gowenrw/BSidesDFW_2019_Badge/eda/BSidesDFW_2019/3d_models/README.md

# 3d_models

This directory is for .STEP and .WRL model files for all footprints
