gowenrw/BSidesDFW_2019_Badge/eda/BSidesDFW_2019/gerber/README.md

# gerber

This directory is for the gerber formatted files to be sent to manufacturing
