gowenrw/BSidesDFW_2019_Badge/eda/BSidesDFW_2019/lib_fp/README.md

# lib_fp

This directory is for footprints

This local library contains footprints for the components used as well as the silkscreen art.
