gowenrw/BSidesDFW_2019_Badge/eda/BSidesDFW_2019/lib_sh/README.md

# lib_sch

This directory is for schematic symbols
