gowenrw/BSidesDFW_2019_Badge/eda/BSidesDFW_2019/pdf/BSidesDFW_2019-as_built-red.gif

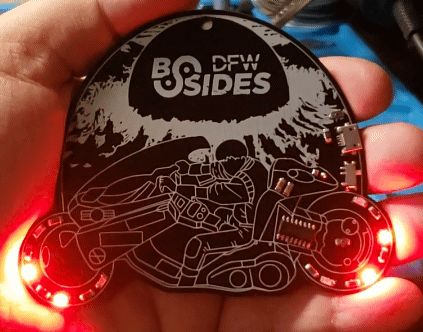
eda/BSidesDFW_2019/pdf/BSidesDFW_2019-as_built-red.gif
