gowenrw/BSidesDFW_2019_Badge/eda/BSidesDFW_2019/pdf/BSidesDFW_2019-as_built.jpg

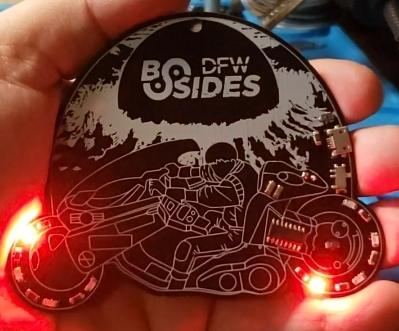
eda/BSidesDFW_2019/pdf/BSidesDFW_2019-as_built.jpg
