gowenrw/BSidesDFW_2019_Badge/eda/BSidesDFW_2019/pdf/BSidesDFW_2019_Back_Bare.png

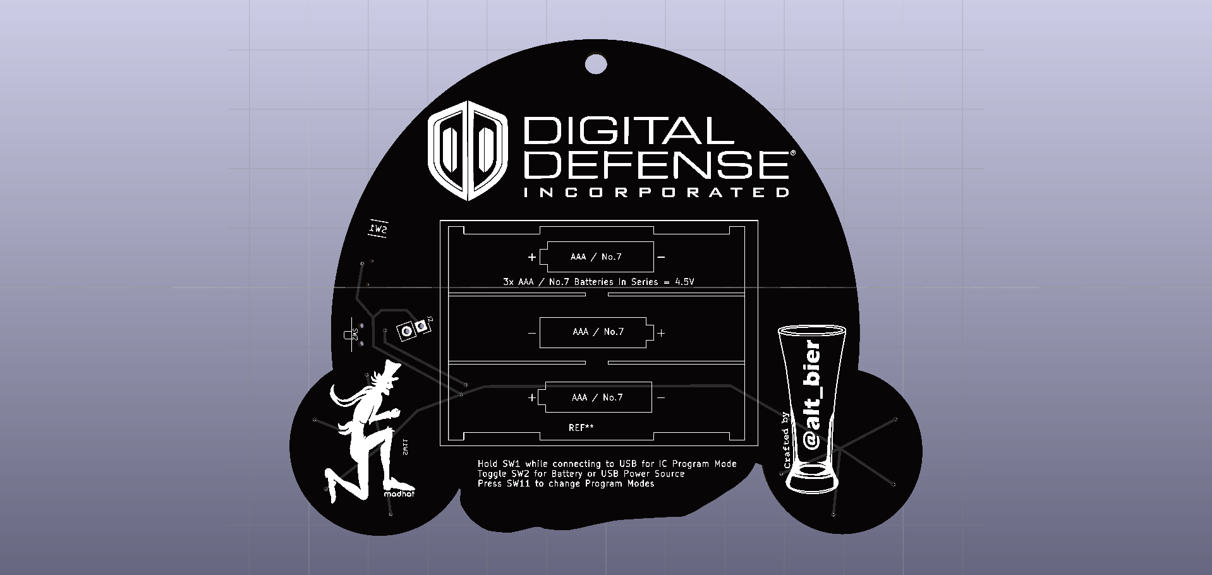
eda/BSidesDFW_2019/pdf/BSidesDFW_2019_Back_Bare.png
