gowenrw/BSidesDFW_2019_Badge/eda/BSidesDFW_2019/pdf/BSidesDFW_2019_Front_Bare.png

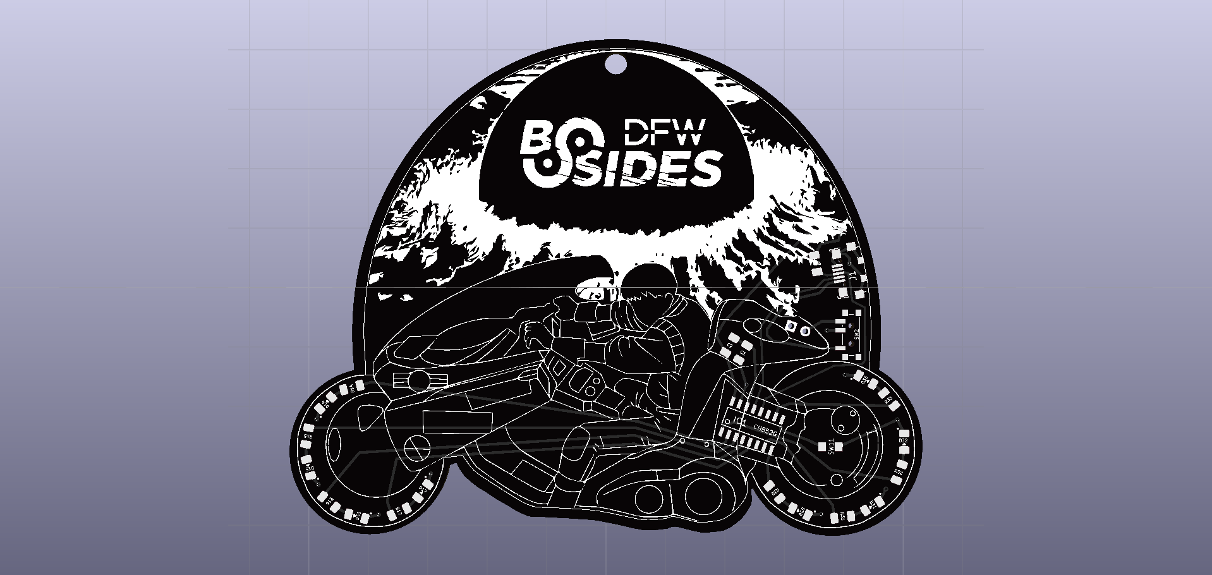
eda/BSidesDFW_2019/pdf/BSidesDFW_2019_Front_Bare.png
