gowenrw/BSidesDFW_2019_Badge/eda/BSidesDFW_2019/pdf/BSidesDFW_2019_pcb-layout_all-layers.png

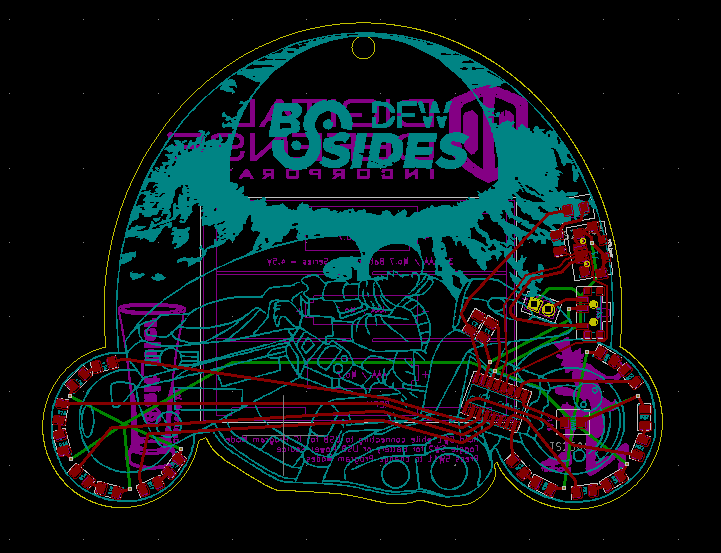
eda/BSidesDFW_2019/pdf/BSidesDFW_2019_pcb-layout_all-layers.png
