gowenrw/BSidesDFW_2019_Badge/eda/CH552G_dev/pdf/CH552G_dev.jpg

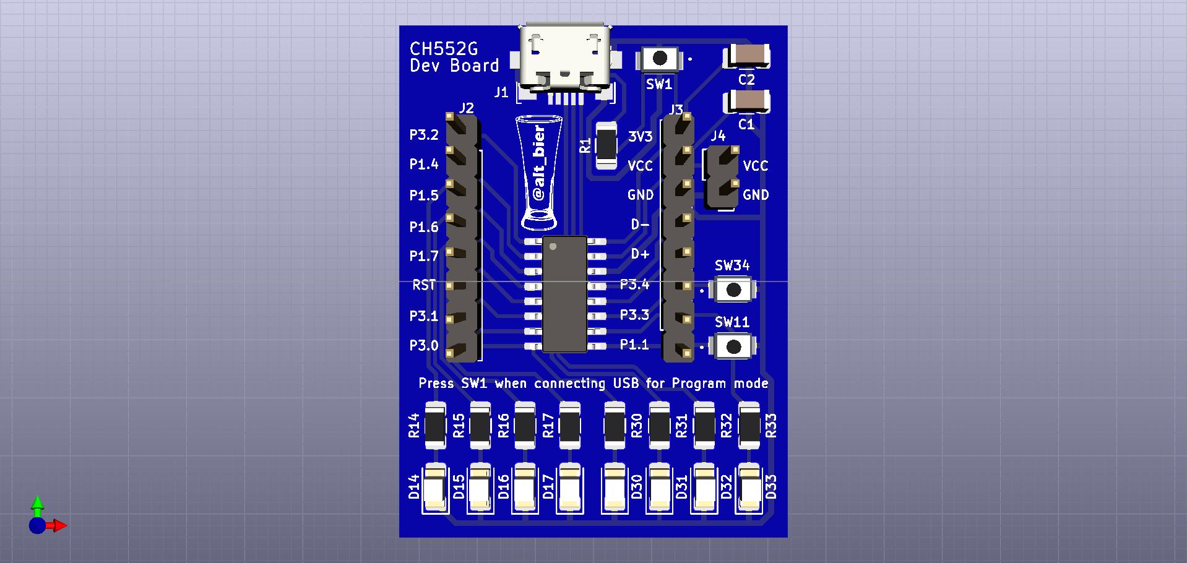
eda/CH552G_dev/pdf/CH552G_dev.jpg
