gowenrw/BSidesDFW_2019_Badge/eda/CH552G_dev/pdf/CH552G_dev_board-as_built-green.gif

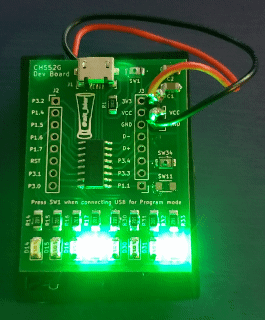
eda/CH552G_dev/pdf/CH552G_dev_board-as_built-green.gif
