gowenrw/BSidesDFW_2019_Badge/eda/HHV_2019_SC/pdf/HHV_2019_SC-as_built.jpg

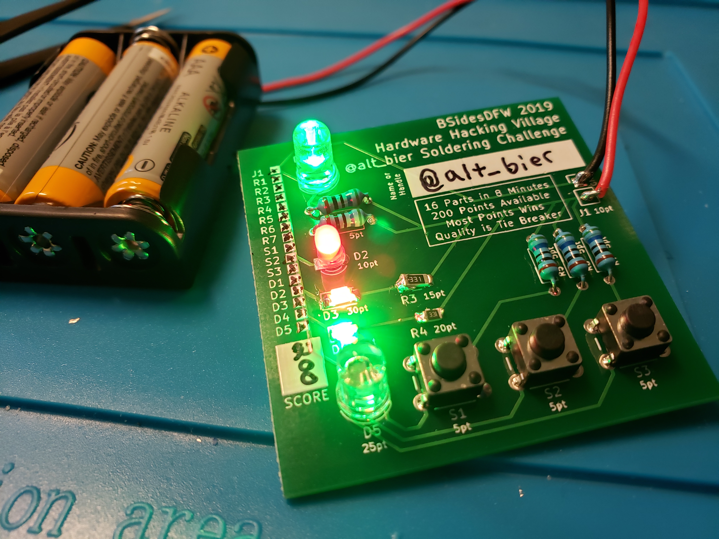
eda/HHV_2019_SC/pdf/HHV_2019_SC-as_built.jpg
