gowenrw/BSidesDFW_2019_Badge/graphics/Asset 1.png

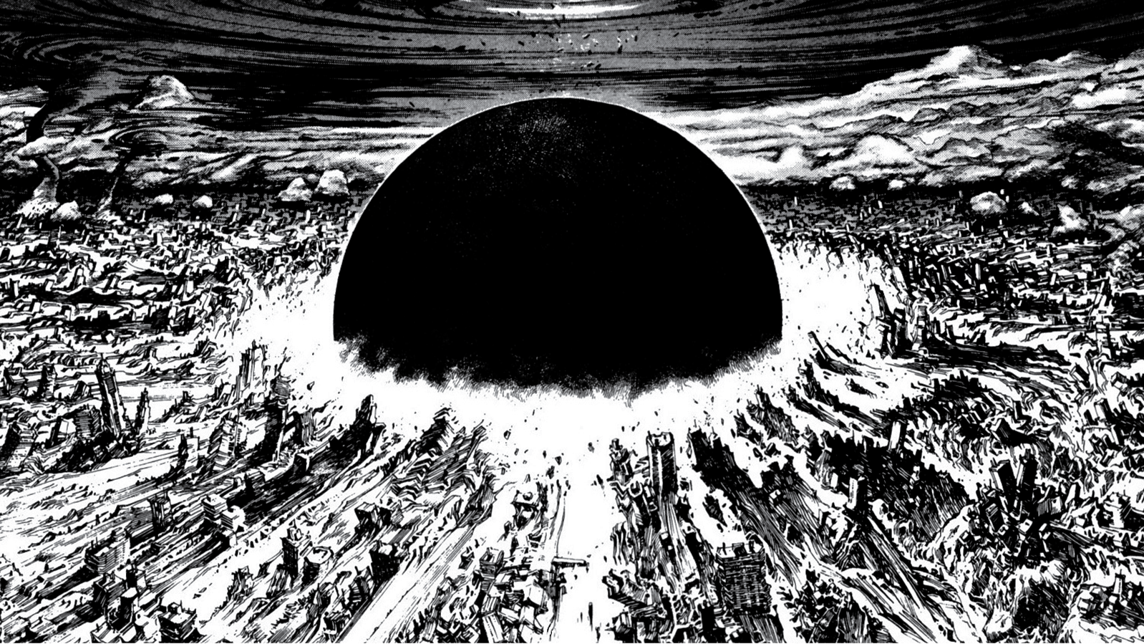
graphics/Asset 1.png
