gowenrw/BSidesDFW_2019_Badge/graphics/Asset 2.png

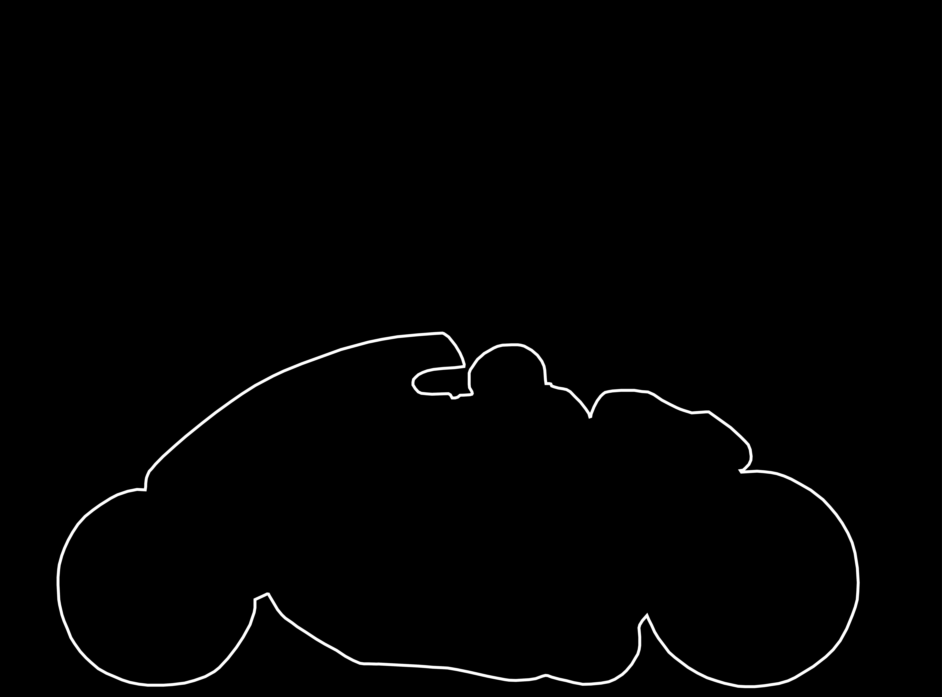
graphics/Asset 2.png
