gowenrw/BSidesDFW_2019_Badge/graphics/Asset 3.png

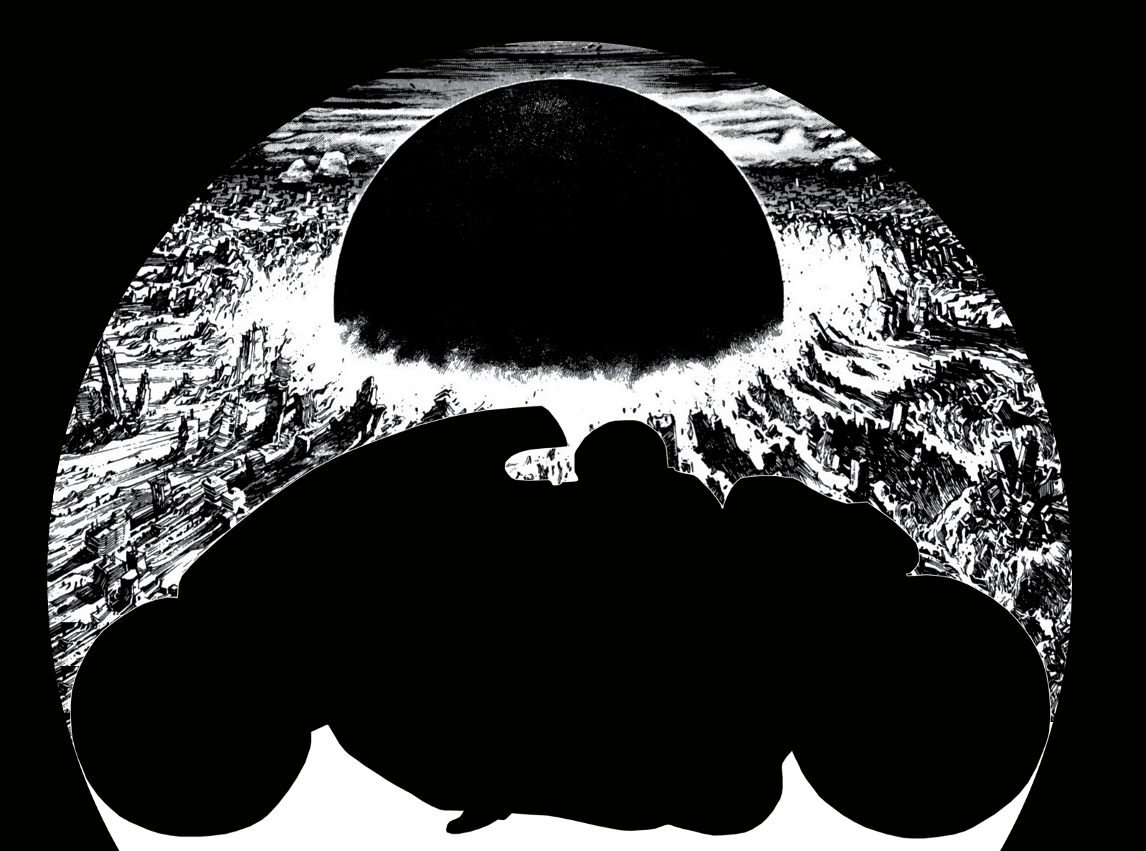
graphics/Asset 3.png
