gowenrw/BSidesDFW_2019_Badge/graphics/BSidesDFW2019_Lanyand-01.jpg

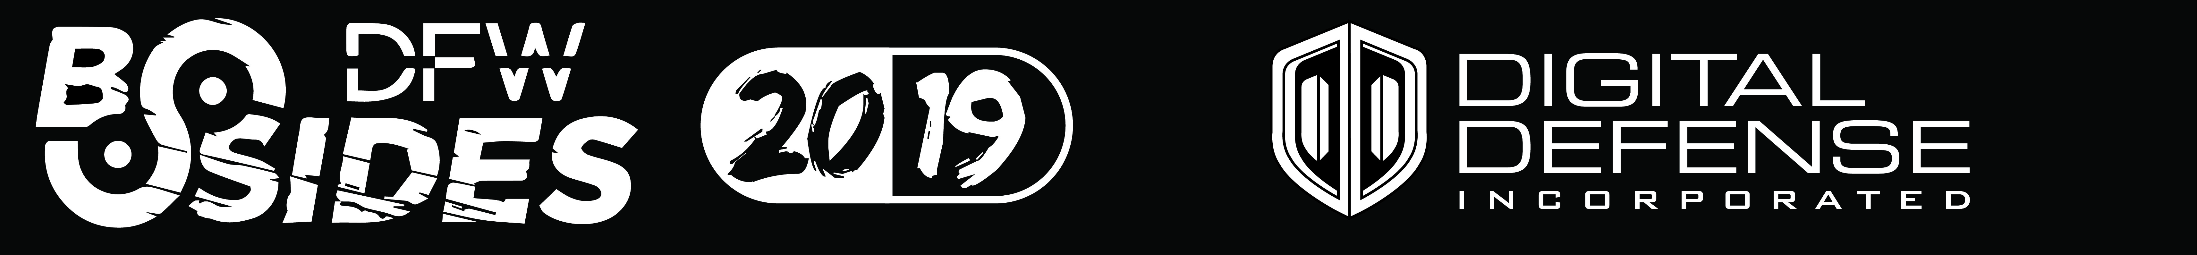
graphics/BSidesDFW2019_Lanyand-01.jpg
