gowenrw/BSidesDFW_2019_Badge/graphics/BSidesDFW2019_Lanyand-a.jpg

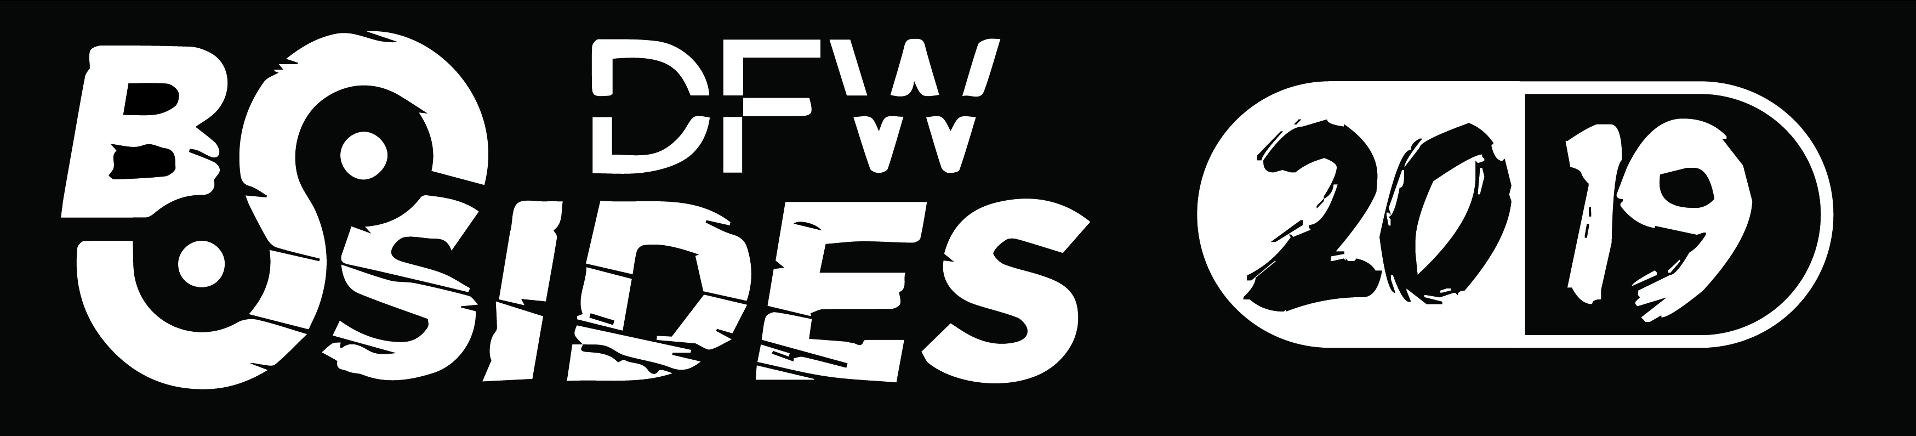
graphics/BSidesDFW2019_Lanyand-a.jpg
