gowenrw/BSidesDFW_2019_Badge/eda/BSidesDFW_2019/pdf/BSidesDFW_2019_Side_Components.png

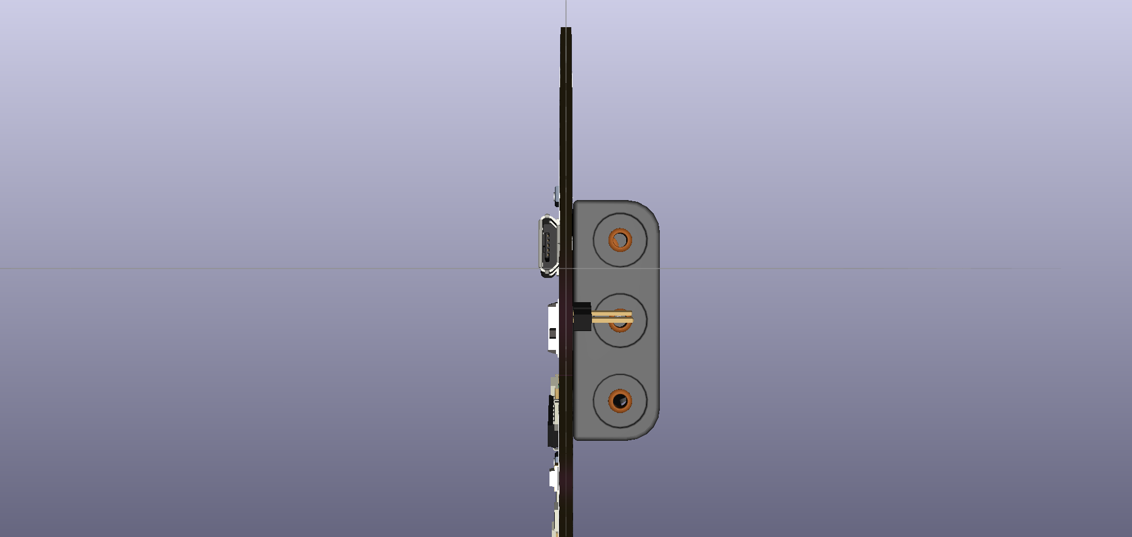
eda/BSidesDFW_2019/pdf/BSidesDFW_2019_Side_Components.png
