gowenrw/BSidesDFW_2019_Badge/eda/HHV_2019_SC/3d_models/LED_D3.0mm.step

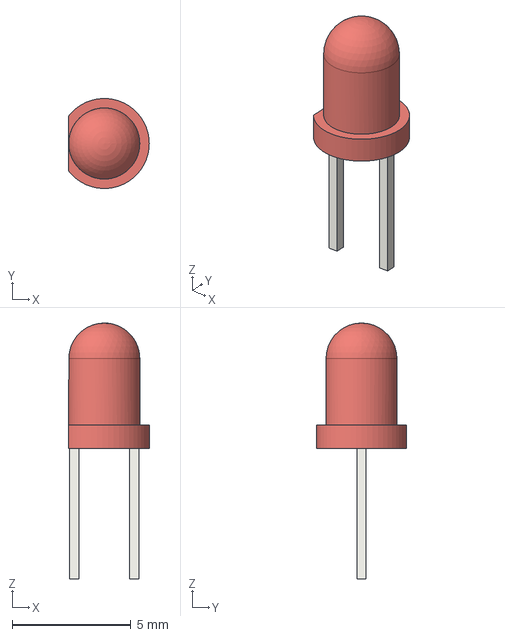
[picture p45: CAD file, 2019-09-09]
eda/HHV_2019_SC/3d_models/LED_D3.0mm.step
3.40 x 3.80 x 10.8 mm
