gowenrw/BSidesDFW_2019_Badge/eda/HHV_2019_SC/3d_models/LED_D8.0mm.step

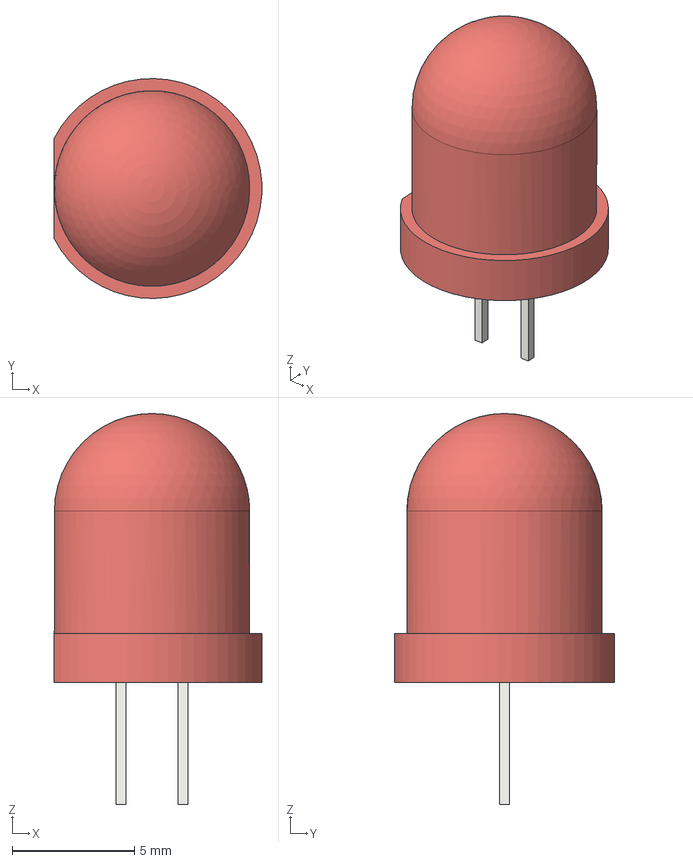
[picture p47: CAD file, 2019-09-09]
eda/HHV_2019_SC/3d_models/LED_D8.0mm.step
8.49 x 9.00 x 16.0 mm
