gowenrw/BSidesDFW_2019_Badge/eda/BSidesDFW_2019/3d_models/C_1206_3216Metric.step

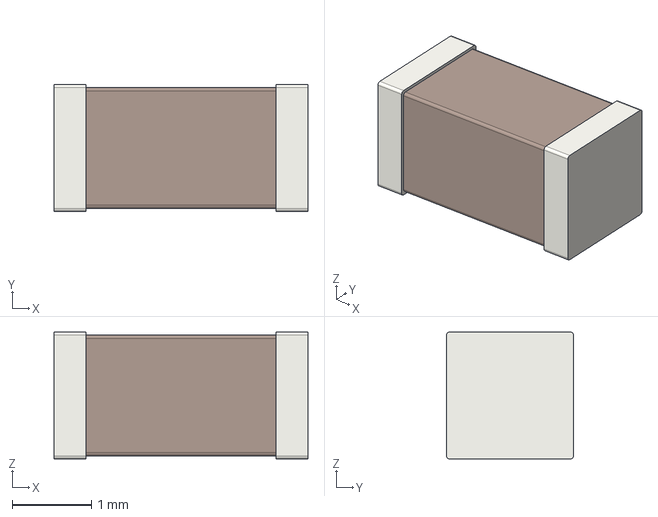
[picture p48: CAD file, 2019-09-05]
eda/BSidesDFW_2019/3d_models/C_1206_3216Metric.step
3.20 x 1.60 x 1.60 mm
