gowenrw/BSidesDFW_2019_Badge/eda/BSidesDFW_2019/3d_models/C_0805_2012Metric.step

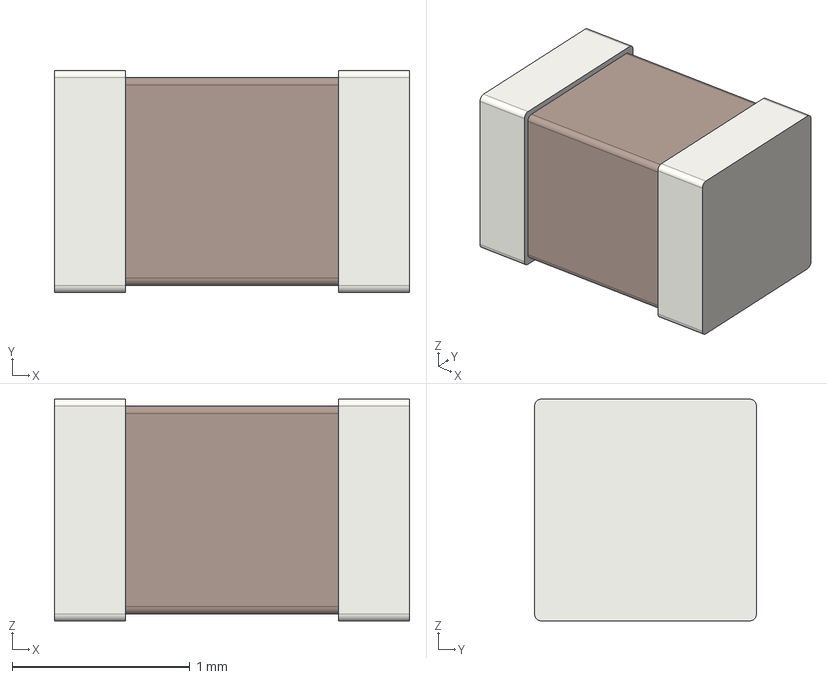
[picture p50: CAD file, 2019-09-05]
eda/BSidesDFW_2019/3d_models/C_0805_2012Metric.step
2.00 x 1.25 x 1.25 mm
