gowenrw/BSidesDFW_2019_Badge/eda/BSidesDFW_2019/3d_models/SOIC-16_3.9x9.9mm_P1.27mm.step

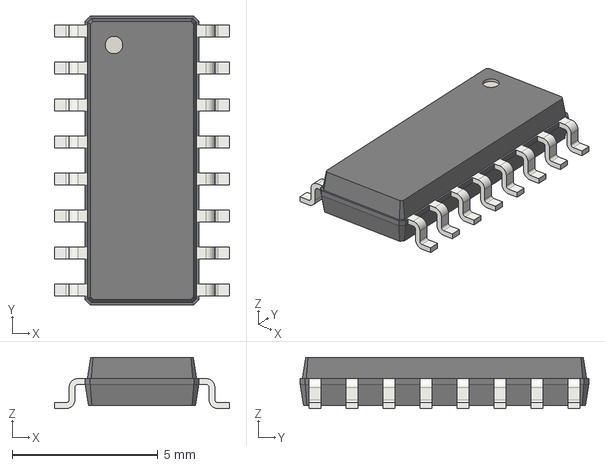
[picture p51: CAD file, 2019-09-05]
eda/BSidesDFW_2019/3d_models/SOIC-16_3.9x9.9mm_P1.27mm.step
6.00 x 9.90 x 1.75 mm
