gowenrw/BSidesDFW_2019_Badge/eda/BSidesDFW_2019/3d_models/R_0805_2012Metric.step

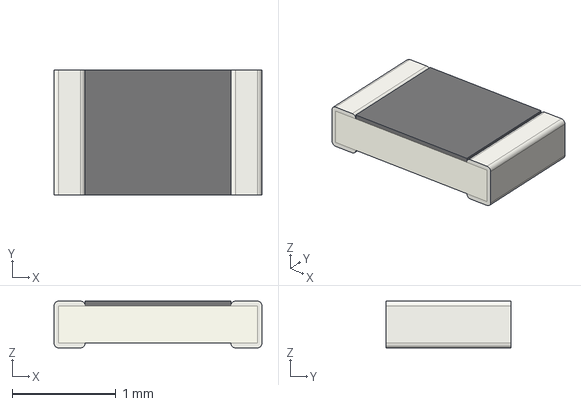
[picture p52: CAD file, 2019-09-05]
eda/BSidesDFW_2019/3d_models/R_0805_2012Metric.step
2.00 x 1.20 x 0.45 mm
