gowenrw/BSidesDFW_2019_Badge/graphics/ugly_dev_board-back.jpg

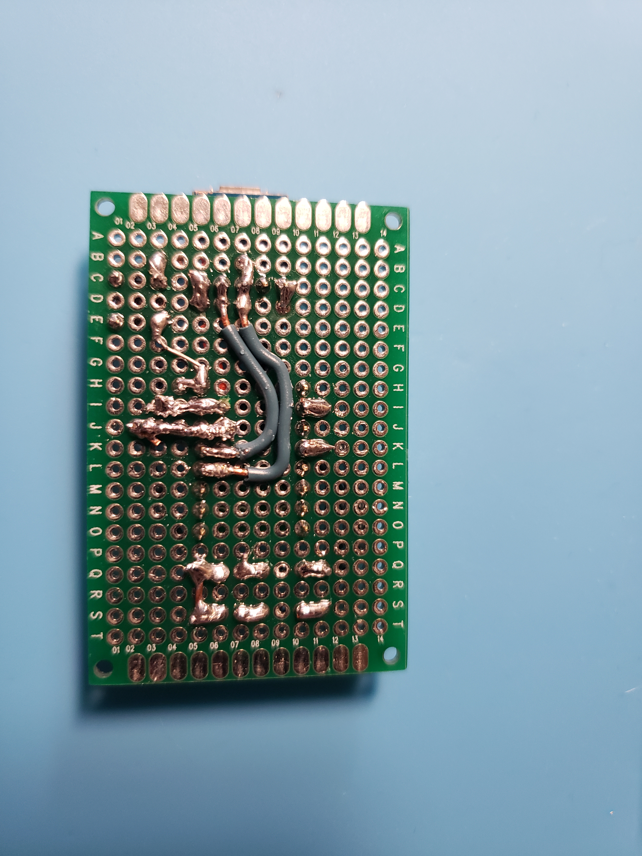
graphics/ugly_dev_board-back.jpg
