gowenrw/BSidesDFW_2019_Badge/graphics/ugly_dev_board-front.jpg

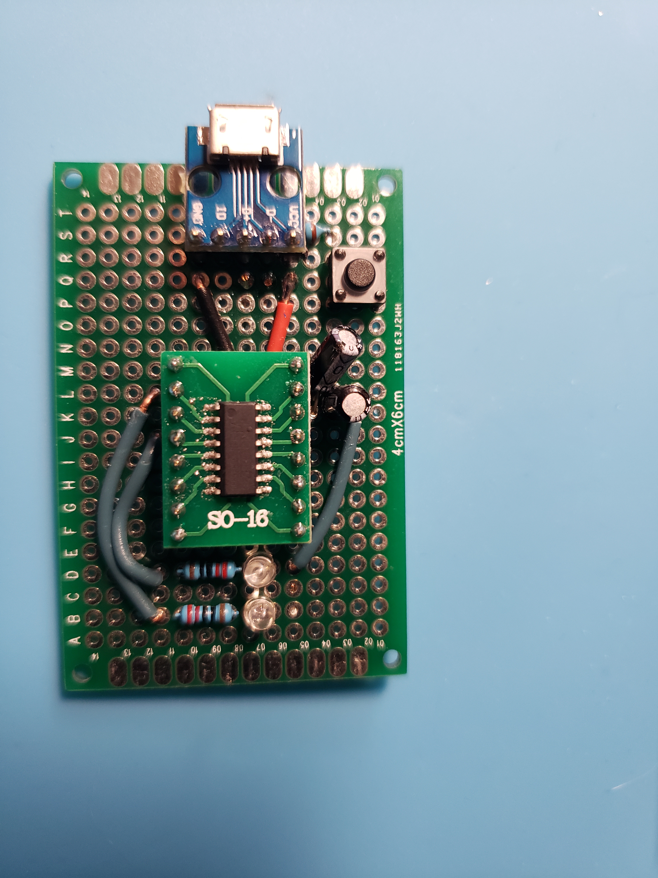
graphics/ugly_dev_board-front.jpg
